Grapes42/Nostalpi_SP/documentation/images/asus_tinker.jpg

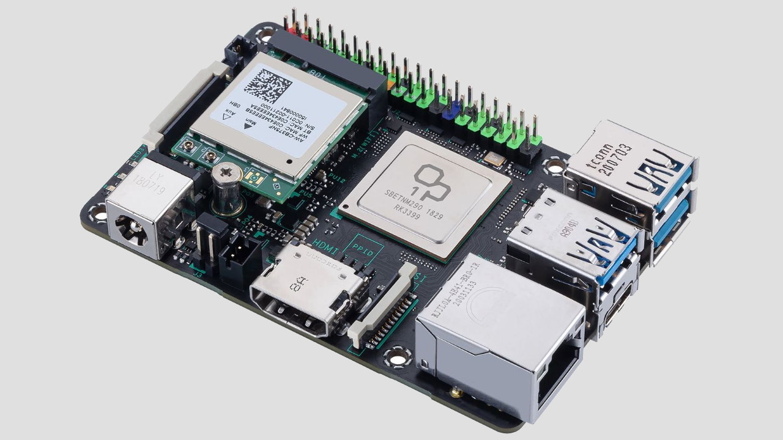
documentation/images/asus_tinker.jpg
