Grapes42/Nostalpi_SP/documentation/images/nostalpi_sp.png

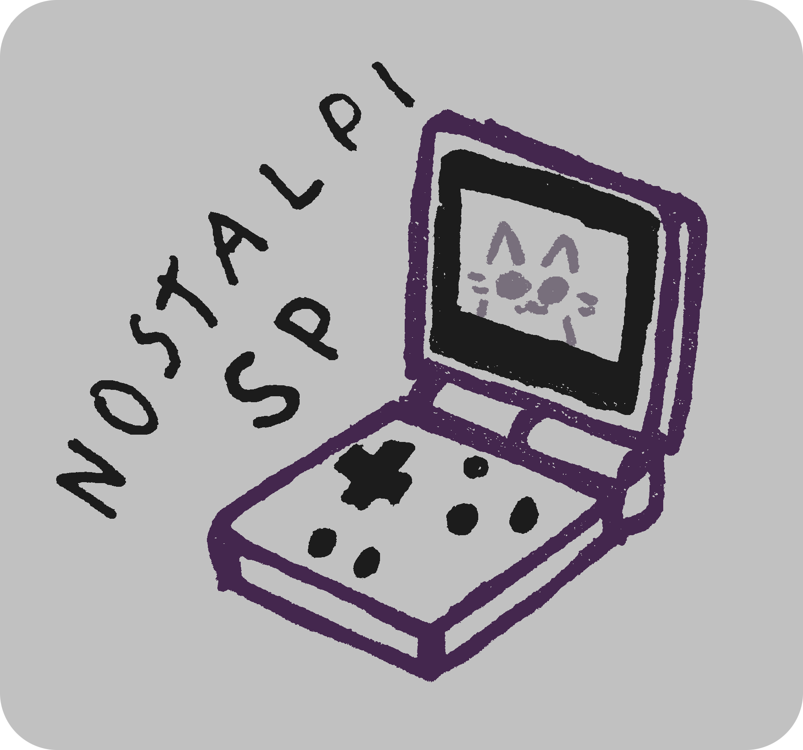
documentation/images/nostalpi_sp.png
