Grapes42/Nostalpi_SP/documentation/images/odroid.jpg

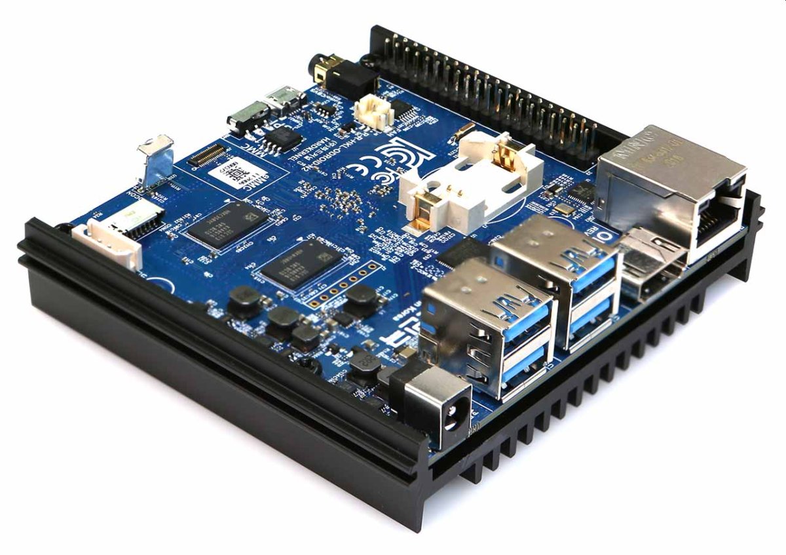
documentation/images/odroid.jpg
