Grapes42/Nostalpi_SP/documentation/images/xperia_play.webp

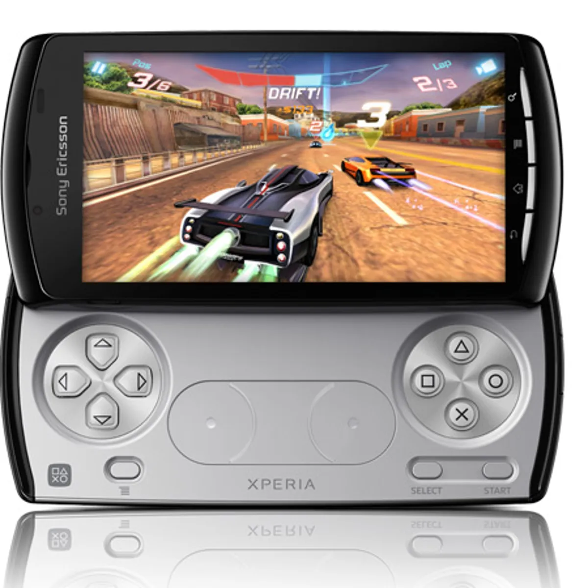
documentation/images/xperia_play.webp
